CuriousTech/WT32-SC01-HVAC/Arduino/WebHandler.cpp

// Do all the web stuff here

#define OTA_ENABLE  //uncomment to enable Arduino IDE Over The Air update code

#include <WiFi.h>
#include <ESPmDNS.h>

#ifdef OTA_ENABLE
#include <ArduinoOTA.h>
#endif
#include <time.h>
#include "WebHandler.h"
#include "HVAC.h"
#include "jsonString.h"
#include "display.h"
#include "eeMem.h"
#include "Media.h"
#include "forecast.h"
#include "Music.h"

//-----------------
int serverPort = 80;

#ifdef REMOTE
#include "WebSocketClient.h"
const char *hostName = RMTNAME;
WebSocketClient WsClient;
bool bWscConnected;
void WscSend(String s);
void startListener(void);
#else
const char *hostName = HOSTNAME;
#endif

extern tm gLTime;
extern Music mus;
AsyncWebServer server( serverPort );
AsyncWebSocket ws("/ws"); // access at ws://[esp ip]/ws

Forecast FC;

//-----------------
extern HVAC hvac;
extern Display display;

void remoteCallback(int8_t iEvent, uint8_t iName, int32_t iValue, char *psValue);

int nWrongPass;
bool bKeyGood;
int WsClientID;
int WsRemoteID;
IPAddress lastIP;
IPAddress WsClientIP;

bool bSmartEnabled;
bool bConfigDone = false; // EspTouch done or creds set
bool bStarted = false;
bool bReconnectWebSocket = false;

#ifdef REMOTE
const char *jsonListSettings[] = { "cmd",
  "m", "am", "hm", "fm", "ot", "ht", "c0", "c1", "h0", "h1", "im", "cn", "cx", "ct", "tu", "ov", "rhm", "rh0", "rh1", NULL
};
const char *jsonListState[] = { "cmd",
  "r", "fr", "s", "it", "rh", "tt", "fm", "ot", "ol", "oh", "ct", "ft", "rt", "h", "lt", "lh", "rmt", "note", NULL
};

#else
const char *jsonListSettings[] = { "cmd", "m", "am", "hm", "fm", "ot", "ht", "c0", "c1", "h0", "h1", "im", "cn", "cx", "ct", "tu", "ov", "rhm", "rh0", "rh1", "rmttemp", "rmtrh", NULL };
#endif
extern const char *cmdList[];

void onWsEvent(AsyncWebSocket * server, AsyncWebSocketClient * client, AwsEventType type, void * arg, uint8_t *data, size_t len)
{  //Handle WebSocket event
  static bool rebooted = true;

  switch(type)
  {
    case WS_EVT_CONNECT:      //client connected
      if(rebooted)
      {
        rebooted = false;
        client->text( "{\"cmd\":\"alert\",\"text\":\"Restarted\"}" );
      }
      client->text( hvac.settingsJson() );
      client->text( dataJson() );
      break;
    case WS_EVT_DISCONNECT:    //client disconnected
    case WS_EVT_ERROR:    //error was received from the other end
#ifndef REMOTE
      if(hvac.m_bRemoteStream && client->id() == WsRemoteID) // stop remote
      {
        hvac.m_bRemoteStream = false;
        hvac.m_notif = Note_RemoteOff;
      }
#endif
      break;
    case WS_EVT_PONG:    //pong message was received (in response to a ping request maybe)
      break;
    case WS_EVT_DATA:  //data packet
      AwsFrameInfo * info = (AwsFrameInfo*)arg;
      if(info->final && info->index == 0 && info->len == len){
        //the whole message is in a single frame and we got all of it's data
        if(info->opcode == WS_TEXT){
          data[len] = 0;
          bKeyGood = false; // for callback (all commands need a key)
          WsClientID = client->id();
          WsClientIP = client->remoteIP();
          FC.JsonParse((char *)data, 0, cmdList, remoteCallback);
        }
      }
      break;
  }
}

void setDamper(bool bOpen)
{
  static bool bIsOpen;

  if(bOpen == bIsOpen)
    return;

  bIsOpen = bOpen;
  String s = "s?key=";
  s += ee.password;
  s += "&";
  s += bOpen ? "half":"close";
  s += "=0";
  FC.start("damper.local", 80, s);
}

// Array of days in each month (non-leap year)
const uint8_t days_per_month[] = { 31, 28, 31, 30, 31, 30, 31, 31, 30, 31, 30, 31 };

uint32_t makeLocalTime32(struct tm *tm_ptr)
{
  // 1. Calculate years since 1970
  // tm_year is years since 1900, so subtract 70 to get years since 1970
  int32_t year = tm_ptr->tm_year - 70; 

  // 2. Count leap days for preceding years
  // Account for the shift in the leap year cycle
  int32_t leap_days = (year + 2) / 4 - (year + 69) / 100 + (year + 369) / 400;

  // 3. Calculate total days from years
  int32_t total_days = year * 365 + leap_days;

  // 4. Add days of the current year up to the current month
  for (int i = 0; i < tm_ptr->tm_mon; ++i) {
      total_days += days_per_month[i];
  }

  // Account for current year being a leap year (Feb gets +1 day)
  // Shifted year calculation matches leap year rules for standard Gregorian calendar
  if (tm_ptr->tm_mon > 1) {
      int32_t absolute_year = tm_ptr->tm_year + 1900;
      if ((absolute_year % 4 == 0 && absolute_year % 100 != 0) || (absolute_year % 400 == 0)) {
          total_days += 1; 
      }
  }

  // 5. Add days of the current month
  total_days += (tm_ptr->tm_mday - 1);

  // 6. Calculate total seconds
  uint32_t local_seconds = (total_days * 86400UL) + 
                           (tm_ptr->tm_hour * 3600UL) + 
                           (tm_ptr->tm_min * 60UL) + 
                           tm_ptr->tm_sec;

  return local_seconds;
}

void startServer()
{
  WiFi.hostname(hostName);
  WiFi.mode(WIFI_STA);
  
  if ( ee.szSSID[0] )
  {
    WiFi.begin(ee.szSSID, ee.szSSIDPassword);
    WiFi.setHostname(hostName);
    hvac.m_notif = Note_Connecting;
    WiFi.setTxPower(WIFI_POWER_8_5dBm);
  }
  else
  {
    hvac.m_notif = Note_EspTouch;
    WiFi.beginSmartConfig();
    bSmartEnabled = true;
  }

  // attach AsyncWebSocket
  ws.onEvent(onWsEvent);
  server.addHandler(&ws);
#ifndef REMOTE

  server.on ( "/", HTTP_GET | HTTP_POST, [](AsyncWebServerRequest *request){
    request->send(INTERNAL_FS, "/index.html");
  });

  // For quick commands, sensors. Remotes have a seperate command list
  server.on ( "/s", HTTP_GET | HTTP_POST, [](AsyncWebServerRequest *request){
    parseParams(request);

    jsonString js;
    static int32_t tzOffset;

    if(tzOffset > -2 && tzOffset < 2) // might be 1 sec off before TZ set
    {
      tzOffset = (int32_t)( makeLocalTime32(&gLTime) - time(nullptr));
    }
    js.Var("tzoffset", tzOffset );
    js.Var("time", time(nullptr));
    js.Var("outtemp", hvac.m_outTemp);
    js.Var("outrh", hvac.m_outRh);
    request->send ( 200, "text/html", js.Close() );
  });

#endif
  server.on("/heap", HTTP_GET, [](AsyncWebServerRequest * request) { // just for checking
    request->send(200, "text/plain", String(ESP.getFreeHeap()));
  });

  server.on ( "/upload", HTTP_POST, [](AsyncWebServerRequest * request)
  {
    request->send( 200);
    ws.textAll(hvac.settingsJson()); // update free space
  },
  [](AsyncWebServerRequest *request, String filename, size_t index, uint8_t *data, size_t len, bool final) {
    if(!index)
      request->_tempFile = media.createFile(filename);
    if(len)
     request->_tempFile.write((byte*)data, len);
    if(final)
      request->_tempFile.close();
   }
  );

  server.serveStatic("/", INTERNAL_FS, "/");
  server.begin();

#ifdef OTA_ENABLE
  ArduinoOTA.setHostname(hostName);
  ArduinoOTA.begin();
  ArduinoOTA.onStart([]() {
    jsonString js("alert");
    js.Var("text", "OTA Update Started");
    ws.textAll(js.Close());
    ws.closeAll();
    hvac.m_notif = Note_Updating; // Display a thing
    display.updateNotification(true);
    hvac.shutdown();
  });
#endif
}

#ifdef REMOTE
void findHVAC() // find the HVAC on iot domain
{
  int cnt = MDNS.queryService("iot", "tcp");
  for(int i = 0; i < cnt; ++i)
  {
    char szName[38];
    MDNS.hostname(i).toCharArray(szName, sizeof(szName));
    strtok(szName, "."); // remove .local

    if(!strcmp(szName, HOSTNAME))
    {
#if ESP_ARDUINO_VERSION >= ESP_ARDUINO_VERSION_VAL(3, 0, 0)
      ee.hostIp[0] = MDNS.address(i)[0]; // update IP
      ee.hostIp[1] = MDNS.address(i)[1];
      ee.hostIp[2] = MDNS.address(i)[2];
      ee.hostIp[3] = MDNS.address(i)[3];
#else
      ee.hostIp[0] = MDNS.IP(i)[0]; // update IP
      ee.hostIp[1] = MDNS.IP(i)[1];
      ee.hostIp[2] = MDNS.IP(i)[2];
      ee.hostIp[3] = MDNS.IP(i)[3];
#endif
      hvac.m_notif = Note_HVACFound;
      break;
    }
  }
}
#endif

void handleServer()
{
#ifdef REMOTE
  if(bReconnectWebSocket)
  {
    bReconnectWebSocket = false;
    startListener();
  }
#endif
#ifdef OTA_ENABLE
  ArduinoOTA.handle();
#endif
}

void WsSend(String s) // mostly for debug
{
  ws.textAll(s);
}

void wsPrint(String s)
{
  jsonString js("print");
  js.Var("text", s);
  ws.textAll(js.Close());
}

bool secondsServer() // called once per second
{
  bool bConn = false;
  static uint8_t nCounter = 5;

  switch(WiFi.status())
  {
    case WL_CONNECTED:
      if(bSmartEnabled && WiFi.smartConfigDone())
      {
        bSmartEnabled = false;
        WiFi.SSID().toCharArray(ee.szSSID, sizeof(ee.szSSID)); // Get the SSID from SmartConfig or last used
        WiFi.psk().toCharArray(ee.szSSIDPassword, sizeof(ee.szSSIDPassword) );
      }

      if(bStarted)
        break;
      bStarted = true;
      WiFi.mode(WIFI_STA); // Stop broadcasting SSID
      MDNS.begin( hostName );
      MDNS.addService("iot", "tcp", serverPort);
      hvac.m_notif = Note_Connected;
      bConn = true;
#ifdef REMOTE
      findHVAC();
#endif
      break;
    case WL_CONNECT_FAILED:
    case WL_NO_SSID_AVAIL: // failed to connect for some reason
      if(bSmartEnabled == false)
      {
        WiFi.mode(WIFI_AP_STA);
        WiFi.beginSmartConfig();
        bSmartEnabled = true;
      }
      break;
    case WL_CONNECTION_LOST:
      break;
    case WL_DISCONNECTED: // connected before and stopped
    case WL_IDLE_STATUS:
      {
        static uint8_t nDelay = 15;
        if(--nDelay == 0)
        {
          WiFi.begin(ee.szSSID, ee.szSSIDPassword); // esp8266 doesn't like it fast
          nDelay = 15;
        }
      }
      break;
    default:
      return bConn;
  }

  ws.cleanupClients();
  static uint8_t nUpdateDelay = 5; // startup delay of 5s, then used for reattempts (60s)
  if(nUpdateDelay)
    nUpdateDelay--;

  if(time(nullptr) >= FC.m_fc.loadDate + (3600*3) && (nUpdateDelay == 0) ) // > 3 hours old
  {
    FC.m_bUpdateFcst = true;
  }

#ifdef REMOTE

  static uint8_t start = 4; // give it time to settle before initial connect
  if(start)
    if(--start == 0)
        startListener();

  if(FC.m_bUpdateFcst && bWscConnected && (nUpdateDelay == 0))
  {
    FC.m_bUpdateFcst = false;
    FC.m_bUpdateFcstIdle = false;
    nUpdateDelay = 60;
    WscSend("{\"bin\":1}"); // request forcast data
  }
#else  // !Remote
  String s = hvac.settingsJsonMod(); // returns "{}" if nothing has changed
  if(s.length() > 2)
    ws.textAll(s); // update anything changed

  if(hvac.stateChange() || hvac.tempChange())
    ws.textAll( dataJson() );

  if(nWrongPass)
    nWrongPass--;

  if(FC.m_bUpdateFcst && FC.m_bUpdateFcstIdle && nUpdateDelay == 0 && gLTime.tm_year > 124)
  {
    FC.m_bUpdateFcst = false;
    FC.m_bUpdateFcstIdle = false;
    nUpdateDelay = 60; // delay retries by 1 minute
    IPAddress hostIp(ee.hostIp);

    switch(ee.b.nFcstSource)
    {
      case 1:
        FC.start(hostIp, ee.hostPort, ee.b.bCelcius, 0);    // get preformatted data from local server
      case 0:
        FC.start(hostIp, ee.hostPort, ee.b.bCelcius, 1);    // get OpenWeatherMap file from local server
        break;
      case 2:
        FC.start(ee.cityID, ee.b.bCelcius);    // get data from OpenWeatherMap 5 day
        break;
    }
  }

  int stat = FC.checkStatus();
  if(stat == FCS_Fail)
  {
    jsonString js("alert");
    js.Var("text", "Forecast failed");
    hvac.m_notif = Note_Forecast;
    WsSend(js.Close());
  }
  else if(stat == FCS_Done)
  {
    display.m_bShowFC = true;
  }
#endif // !REMOTE
  return bConn;
}

#ifndef REMOTE
void parseParams(AsyncWebServerRequest *request)
{
  if(request->params() == 0)
    return;

  bool bPassGood;

  IPAddress ip = request->client()->remoteIP();

  for ( uint8_t i = 0; i < request->params(); i++ )
  {
    const AsyncWebParameter* p = request->getParam(i);
    String s = request->urlDecode(p->value());

    if(p->name() == "key")
    {
      bPassGood = s.equals(ee.password);
      if(!bPassGood)
      {
        if(nWrongPass == 0)
        {
          nWrongPass = 10;
          jsonString js("hack");
          js.Var("ip", ip.toString() );
          ws.textAll(js.Close());
        }
        else if((nWrongPass & 0xFFFFF000) == 0 ) // time doubles for every high speed wrong password attempt.  Max 1 hour
          nWrongPass <<= 1;
        if(ip != lastIP)  // if different IP drop it down
          nWrongPass = 10;
      }
      lastIP = ip;
    }
    else if(bPassGood)
    {
      if(p->name() == "fc")
        FC.m_bUpdateFcst = true;
      hvac.setVar(p->name(), s.toInt(), (char *)s.c_str(), ip );
    }
  }
}
#endif

// Pushed data
String dataJson()
{
  return hvac.getPushData();
}

void remoteCallback(int8_t iEvent, uint8_t iName, int32_t iValue, char *psValue)
{
  static int8_t cmd = 0;

#ifdef REMOTE

  switch(iName)
  {
    case 0: // cmd
      if(!strcmp(psValue, "settings"))
      {
        FC.setList(jsonListSettings);
        cmd = 1;
      }
      else if(!strcmp(psValue, "state"))
      {
        FC.setList(jsonListState);
        cmd = 2;
      }
      break;
    case 1: // key (from page)
//      FC.setList(jsonListSettings);
//      cmd = 1;
      break;
  }
  if(iName) switch(cmd)
  {
    case 0:
    case 1: //settings
      hvac.setSettings(iName - 1, iValue);
      break;
    case 2: // state
      hvac.updateVar(iName - 1, iValue);
      break;
  }

#else //!REMOTE
  switch(cmd) // Should always be 0
  {
    case 0: // key
      if(iName == 1) // 0 = key
      {
        if(!strcmp(psValue, ee.password)) // first item must be key
        {
          bKeyGood = true;
        }
      }
      else if(iName == 2) //data
      {
        uint16_t idx = constrain(iValue, 0, GPTS-1);
        if(display.m_points[idx].t.u) // only send if valid
          ws.binary(WsClientID, (uint8_t *)&display.m_points[idx], sizeof(gPoint));
      }
      else if(iName == 3) // 3 = sum
      {
        uint32_t (*pSecsMon)[3] = hvac.m_SecsMon;
        uint16_t (*pSecsDay)[3] = hvac.m_SecsDay;

        uint16_t tempSecsDay[32][3];
        uint32_t tempSecsMon[12][3];

        uint8_t mon = iValue & 0xF;
        uint16_t yr = (iValue >> 4) & 0xFFF;

        if(mon && mon != gLTime.tm_mon+1) // month is 1-12, so 0 can be used as current
        {
          String sName = "/statsday"; // decode requested file
          sName += yr;
          sName += ".";
          sName += mon;
          sName += ".dat";

          File F;
          if(F = INTERNAL_FS.open(sName) )
          {
            F.read((byte*)&tempSecsDay, sizeof(tempSecsDay)); // read the requested daily file
            F.close();
            pSecsDay = tempSecsDay;
          }

          if(yr != gLTime.tm_year+1900) // not currrent year
          {
            sName = "/statsmonth";
            sName += yr;
            sName += ".dat";
            if(F = INTERNAL_FS.open(sName) )
            {
              F.read((byte*)&tempSecsMon, sizeof(tempSecsMon)); // read the requested yearly file
              F.close();
              pSecsMon = tempSecsMon;
            }
          }
        }

        jsonString js("sum");
        js.Array3("mon", pSecsMon, 12);
        js.Array3("day", pSecsDay, 31);
        js.Var("idx", display.m_pointsIdx);
        js.Var("tb", display.m_lastPDate);
        js.Var("th", ee.cycleThresh[ (hvac.m_modeShadow == Mode_Heat) ? 1:0]); // threshold
        js.Var("fcDate", FC.m_fc.Date);
        js.Var("fcFreq", FC.m_fc.Freq);

        int16_t arr[FC_CNT][3];
        uint8_t cnt;
        for(cnt = 0; FC.m_fc.Data[cnt].temp != -1000 && cnt < FC_CNT; cnt++)
        {
          arr[cnt][0] = FC.m_fc.Data[cnt].temp;
          arr[cnt][1] = FC.m_fc.Data[cnt].feelsLike;
          arr[cnt][2] = FC.m_fc.Data[cnt].humidity;
        }
        js.Array3("fc", arr, cnt);

        ws.text(WsClientID, js.Close());
      }
      else if(iName == 4) // 4 = bin
      {
        WsRemoteID = WsClientID; // Only remote uses binary
        switch(iValue)
        {
          case 0: // backward compatible forecast data (can't be done easily)
            break;
          case 1: // new forecast data
            ws.binary(WsClientID, (uint8_t*)&FC.m_fc, sizeof(FC.m_fc));
            break;
          case 2: // temp points
            ws.binary(WsClientID, (uint8_t *)display.m_points, sizeof(display.m_points));
            break;
        }
      }
      else if(bKeyGood && iName >= 5)
      {
        hvac.setVar(cmdList[iName], iValue, psValue, WsClientIP); // 5 is "fanmode"
      }
      break;
    case 2: // state
      switch(iName)
      {
        case 0: // temp
          hvac.setVar("rmttemp", iValue, psValue, WsClientIP);
          break;
        case 1: // rh
          hvac.setVar("rmtrh", iValue, psValue, WsClientIP);
          break;
      }
      break;
  }

#endif
}

#ifdef REMOTE

// Remote websocket client
void WscSend(String s) // remote WebSocket
{
  if(!bWscConnected)
    return;
  WsClient.send(s);
}

void webSocketEventHandler(uint8_t event, char *data, uint16_t length)
{
  static bool bFirst = true;

  switch(event)
  {
    case WEBSOCKET_EVENT_ERROR:
      break;
    case WEBSOCKET_EVENT_CONNECTED:
      bWscConnected = true;
      FC.m_bUpdateFcst = true; // Get the forecast faster
      FC.m_bUpdateFcstIdle = true;
      if(hvac.m_notif == Note_Network) // remove net disconnect error
        hvac.m_notif = Note_None;
      if(bFirst)
      {
        bFirst = false;
        hvac.m_notif = Note_Connected; // helps see things connecting
      }
      break;
    case WEBSOCKET_EVENT_DISCONNECTED:
      bWscConnected = false;
      hvac.m_notif = Note_Network;
      bReconnectWebSocket = true;
      break;
    case WEBSOCKET_EVENT_DATA_TEXT:
      FC.JsonParse((char *)data, 0, jsonListSettings, remoteCallback);
      break;
    case WEBSOCKET_EVENT_DATA_BINARY:
      if(length != sizeof(FC.m_fc) )
        break;
      memcpy((void*)&FC.m_fc, data, sizeof(FC.m_fc));
      FC.m_fc.loadDate = time(nullptr);
      FC.m_bUpdateFcstIdle = true;
      FC.m_bFcstUpdated = true;
      display.m_bShowFC = true;
      break;
  }
}

void startListener()
{
  IPAddress ip(ee.hostIp);
  WsClient.connect((char *)ip.toString().c_str(), "/ws", 80);
  WsClient.setCallback(webSocketEventHandler);
}
#endif
