CuriousTech/WT32-SC01-HVAC/Arduino/HVAC.h

#ifndef HVAC_H
#define HVAC_H

// Uncomment to build remote
//#define REMOTE

#define HOSTNAME "HVAC" // Main unit name, remote will search for this
#define RMTNAME "Remote1"

//  HVAC Control
//----------------
#define P_FAN    5 // G GPIO for SSRs
#define P_COOL  27 // Y
#define P_REV   25 // O
#define P_HEAT  26 // W
#define P_HUMID 32 // H
#define SPEAKER 33
#define FAN_ON    LOW
#define FAN_OFF   HIGH
#define COOL_ON   LOW
#define COOL_OFF  HIGH
#define HEAT_ON   LOW
#define HEAT_OFF  HIGH
#define REV_ON    LOW
#define REV_OFF   HIGH
#define HUMID_ON  LOW
#define HUMID_OFF HIGH
//-----------------
#include <Arduino.h>

enum Mode
{
  Mode_Off,
  Mode_Cool,
  Mode_Heat,
  Mode_Auto,
  Mode_Fan,
  Mode_Humid
};

enum FanMode
{
  FM_Auto,
  FM_On
};

enum Notif
{
  Note_None,
  Note_Connecting,
  Note_Connected,
  Note_Serching,
  Note_RemoteOff,
  Note_RemoteOn,
  Note_CycleLimit,
  Note_Network, // Sound errors below this point
  Note_Forecast,
  Note_Filter,
  Note_EspTouch,
  Note_Sensor,
  Note_HVACFound,
  Note_Updating,
  Note_HPHeatError,
  Note_NGHeatError,
  Note_CoolError,
};

enum HeatMode
{
  Heat_HP,
  Heat_NG,
  Heat_Auto
};

enum State
{
  State_Off,
  State_Cool,
  State_HP,
  State_NG
};

enum HumidifierMode
{
  HM_Off,
  HM_Fan,
  HM_Run,
  HM_Auto1,
  HM_Auto2,
};

enum ScheduleMode
{
  SM_Forecast,
  SM_Sine,
  SM_Flat,
  SM_Reserved
};

struct sensorFlags
{
  uint8_t Weight:3;
  uint8_t currWeight:3;
  uint8_t Warn:1;
};

union usensorFlags
{
  uint32_t val;
  sensorFlags f;
};

struct Sensor
{
  uint32_t tm;
  uint32_t timer; // seconds, priority timer
  uint32_t timerStart;
  uint8_t IP[4];
  usensorFlags f;
  int16_t  temp;
  uint16_t rh;
  char     szName[12];
};

#define SNS_PRI   (1 << 0) // Give extra weight to this sensor
#define SNS_EN    (1 << 1) // Enabled = averaged between all enabled
#define SNS_NEG   (1 << 8)  // From remote or page, set this bit to disable a flag above

class HVAC
{
public:
  HVAC(void);
  void    init(void);             // after EEPROM read
  void    disable(void);          // Shut it off
  void    service(void);          // call once per second
  uint8_t getState(void);         // return current run state simplified (0=off, 1=cool, 2=hp, 4=NG)
  bool    getFanRunning(void);    // return fan running
  uint8_t getMode(void);          // actual mode
  uint8_t getHeatMode(void);      // heat mode
  int8_t  getAutoMode(void);      // get current auto heat/cool mode
  int8_t  getSetMode(void);       // get last requested mode
  void    setMode(int mode);   // request new mode; see enum Mode
  void    setHeatMode(int mode); // heat mode
  int8_t  getFan(void);           // fan mode
  bool    getHumidifierRunning(void);
  uint8_t getHumidifierMode(void);
  void    setHumidifierMode(uint8_t m);
  void    setFan(int8_t m);        // auto/on/s mode
  void    filterInc(void);
  bool    stateChange(void);      // change since last call = true
  int16_t getSetTemp(int mode, int hl); // get temp set for a mode (cool/heat, hi/lo)
  void    setTemp(int mode, int16_t Temp, int hl); // set temp for a mode
  void    enableRemote(void);
  void    updateIndoorTemp(int16_t Temp, int16_t rh);
  void    updateOutdoorTemp(int16_t outTemp, bool boost);
  void    resetFilter(void);    // reset the filter hour count
  bool    checkFilter(void);
  void    resetTotal(void);
  bool    tempChange(void);
  void    setVar(String sCmd, int val, char *psValue, IPAddress ip); // remote settings
  void    updateVar(int iName, int iValue); // host values
  void    setSettings(int iName, int iValue);// remote settings
  String  settingsJson(void); // get all settings in json format
  String  settingsJsonMod(void);
  String  getPushData(void);  // get states/temps/data in json
  void    dayTotals(int d);
  void    monthTotal(int m, int dys);
  void    loadStats(void);
  void    saveStats(void);
  void    override(int val);
  void    shutdown(void);
  void    sendCmd(const char *szName, int value);

  int16_t  m_outTemp;       // adjusted current temp *10
  int16_t  m_outRh;
  int16_t  m_inTemp;        // current indoor temperature *10
  int16_t  m_rh;
  int16_t  m_localTemp;     // this device's temperature *10
  int16_t  m_localRh;
  uint16_t m_targetTemp;    // end temp for cycle
  uint16_t m_startTemp;    // temp at start of cycle
  uint16_t m_endTemp;    // temp at end of cycle
  uint16_t m_filterMinutes;
  uint8_t  m_notif;
  bool     m_bRemoteStream; // remote is streaming temp/rh
  bool     m_bRemoteDisconnect;
  int16_t  m_outMin, m_outMax;
  uint16_t m_iSecs[3];
  int8_t   m_modeShadow = Mode_Cool;  // shadow last valid mode
  int      m_overrideTimer; // countdown for override in seconds

#define SNS_CNT 8
  Sensor   m_Sensor[SNS_CNT]; // remote and sensors

  uint16_t m_daySum, m_monSum;
  uint16_t m_SecsDay[32][3];
  uint32_t m_SecsMon[12][3];

private:
  void  fanSwitch(bool bOn);
  void  humidSwitch(bool bOn);
  void  tempCheck(void);
  bool  preCalcCycle(int16_t tempL, int16_t tempH);
  void  calcTargetTemp(int mode);
  float sineTemp(float offset, int16_t H, int16_t L);
  void  costAdd(int secs, int mode, int hm);
  int   CmdIdx(String s);
  int   getSensorID(IPAddress ip);
  void  swapSensors(int n1, int n2);
  void  shiftSensors(void);
  void  activateSensor(int idx);
  void  deactivateSensor(int idx);

  int8_t  m_FanMode;        // Auto=0, On=1, s=2
  bool    m_bFanRunning;    // when fan is running
  bool    m_bHumidRunning;
  bool    m_bRevOn;         // shadow for reverse valve (ESP-32 digitalRead may not read latch bit)
  int8_t  m_AutoMode;       // cool, heat
  int8_t  m_setMode;        // preemted mode request
  int8_t  m_setHeat;        // preemt heat mode request
  int8_t  m_AutoHeat;       // auto heat mode choice
  bool    m_bRunning;       // is operating
  bool    m_bStart;         // signal to start
  bool    m_bStop;          // signal to stop
  bool    m_bRecheck;       // recalculate target now
  bool    m_bEnabled;       // enables system
  bool    m_bAway;
  uint16_t m_fanPreElap = 60*10;
  uint16_t m_runTotal;      // time HVAC has been running total since reset
  uint32_t m_fanOnTimer;    // time fan is running
  uint16_t m_cycleTimer;    // time HVAC has been running
  uint16_t m_fanPostTimer;  // timer for delay
  uint16_t m_fanPreTimer;   // timer for fan pre-run
  uint16_t m_idleTimer = 3*60; // time not running
  uint32_t m_fanIdleTimer; // time fan not running
  uint16_t m_fanAutoRunTimer; // auto fan time
  int8_t   m_ovrTemp;       // override delta of target
  uint16_t m_remoteTimeout; // timeout for remote sensor
  uint16_t m_remoteTimer;   // in seconds
  uint16_t m_humidTimer;    // timer for humidifier cost
  int8_t   m_furnaceFan;    // fake fan timer (actually half watts)
};

#endif
