CuriousTech/WT32-SC01-HVAC/Arduino/forecast.h

#ifndef FORECAST_H
#define FORECAST_H

#include <Arduino.h>
#include <AsyncTCP.h>

#define APPID "xxxxxxxxxxxxxxxxxxxxxxxxxxxxxxxx" // OpenWeathermap APP ID

#define FC_CNT 72 // Max forecast items

struct forecastItem
{
  int16_t temp;
  int16_t humidity;
  int16_t feelsLike;
  int16_t id;
};

struct forecastData
{
  uint32_t Date;
  uint32_t loadDate;
  uint16_t Freq;
  forecastItem Data[FC_CNT + 2];
};

enum FCS_Status
{
  FCS_Idle,
  FCS_Busy,
  FCS_Done,
  FCS_ConnectError,
  FCS_Fail,
  FCS_MemoryError,
};

struct iconAni
{
  uint8_t icon[8]; // icons per day
  uint16_t x; // weather icon positions
};

class Forecast
{
public:
  Forecast(void);
  void init(void);

  void JsonParse(char *p, int8_t event, const char **jsonList, void (*pcb)(int8_t iEvent, uint8_t iName, int32_t iValue, char *psValue));
  void start(IPAddress serverIP, uint16_t port, bool bCelcius, int8_t type);
  void start(char *pCityID, bool bCelcius); // Openweathermmap start
  void start(char *pszName, uint16_t port, String sUri);
  void setList(const char **jsonList);
  int checkStatus();
  bool getCurrentIndex(int8_t& fcOff, int8_t& fcCnt, uint32_t& tm); // index into stored data at current timeframme
  bool forecastPage(void);
  void forecastAnimate(void);
  void getMinMax(int16_t& tmin, int16_t& tmax, int8_t offset, int8_t range);
  int16_t getCurrentTemp(int& shiftedTemp, uint8_t shiftMins, bool& boost);
  void drawIcon(uint8_t d, uint8_t h, uint16_t x);
private:
  void _onConnect(AsyncClient* client);
  void _onDisconnect(AsyncClient* client);
  void _onData(AsyncClient* client, char* data, size_t len);
  void processOWM(void);
  void processJson(char *p, int8_t event, const char **jsonList);
  int makeroom(uint32_t newTm);
  char *skipwhite(char *p);
  void (*m_pCallback)(int8_t iEvent, uint8_t iName, int32_t iValue, char *psValue);
  void callback(int8_t iEvent, uint8_t iName, int32_t iValue, char *psValue);
  String makeName(uint8_t icon, uint8_t h);
  int tween(int16_t t1, int16_t t2, int m, int r);

  const char **m_pJsonList = NULL;
  AsyncClient m_ac;
  char m_cityID[8];
  char *m_pBuffer = NULL;
  int m_bufIdx;
  int m_fcIdx;
  int m_fcCnt;
  uint32_t m_lastTm;
  bool m_bFirst;
  bool m_bDone = false;
  bool m_bCelcius;
  int m_status;
  bool m_bLocal;
  int8_t m_type;
  iconAni m_fcIcon[7];
  uint8_t m_iconIdx;
  String m_sUri;
public:
  forecastData m_fc;
  bool    m_bUpdateFcst = true;
  bool    m_bUpdateFcstIdle = true;
  bool    m_bFcstUpdated = false;
};

#define OWBUF_SIZE 17500

#endif // FORECAST_H
