CuriousTech/WT32-SC01-HVAC/Arduino/Media.h

#ifndef MEDIA_H
#define MEDIA_H

#include <Arduino.h>
#include <TJpg_Decoder.h>   //https://github.com/Bodmer/TJpg_Decoder
#define FS_NO_GLOBALS
#include <FS.h>

#include <SPIFFS.h> // SPIFFS has no subdirs but takes less code space

#define INTERNAL_FS SPIFFS // Make it the same as the partition scheme uploaded (SPIFFS, LittleFS, FFat)

class Media
{
public:
  Media(void);
  void init(void);

  void deleteFile(char *pszFilename);
  fs::File createFile(String sFilename); //only ESP32 needs this namespace decl
  void createDir(char *pszName);
  void setPath(char *szPath);
  uint32_t freeSpace(void);

  void loadImage(String sName, uint16_t x, uint16_t y);
};

extern Media media;

#endif // MEDIA_H
