CuriousTech/WT32-SC01-HVAC/Arduino/screensavers.h

#ifndef SCREENSAVERS_H
#define SCREENSAVERS_H

#include <Arduino.h>
#include <TFT_eSPI.h>
extern TFT_eSPI tft;
extern TFT_eSprite sprite;

#define DISPLAY_WIDTH 480
#define DISPLAY_HEIGHT 320

enum Saver
{
//  SS_Clock,
  SS_Lines,
  SS_Boing,
  SS_Calendar,
  SS_Count, // Last one
};

struct Line
{
  int16_t x1;
  int16_t y1;
  int16_t x2;
  int16_t y2;
};

struct Ball
{
  int16_t x;
  int16_t y;
  int16_t dx;
  int16_t dy;
  int16_t color;
};


class ScreenSavers
{
#define LINES 50
#define BALLS 8
#define BUFFER_SIZE 1024

static_assert(sizeof(Ball) * BALLS < BUFFER_SIZE, "m_buffer size too small");
static_assert(sizeof(Line) * LINES < BUFFER_SIZE, "m_buffer size too small");

public:
  ScreenSavers(){};
  void select(int n);
  void run(void);

  uint8_t m_saver;
  uint8_t m_buffer[BUFFER_SIZE];
  uint8_t hourFormat12(uint8_t h);
  const char *monthShortStr(uint8_t m);
  const char *monthStr(uint8_t m);
  const char *dayShortStr(uint8_t m);
  String localTimeString();

private:
//  void Clock(bool bInit);
//  void cspoint(uint16_t &x2, uint16_t &y2, uint16_t x, uint16_t y, uint16_t angle, uint16_t size);
  void Lines(bool bInit);
  void Boing(bool bInit);
  void Calendar(bool bInit);
};

#endif // SCREENSAVERS_H
